mirkosertic/ESP8266Weatherstation/src/icons.h

#ifndef ICONS_H
#define ICONS_H

#include <Arduino.h>

// Bitmaps generated with https://javl.github.io/image2cpp/

// Icons with credits to https://github.com/manifestinteractive/weather-underground-icons/tree/master/

const unsigned char epd_bitmap_temperature[] PROGMEM = {
	0xff, 0xff, 0xff, 0xff, 0xff, 0xff, 0xff, 0xff, 0xff, 0xff, 0xff, 0xff, 0xff, 0xff, 0xff, 0xff,
	0xff, 0xf0, 0x3f, 0xff, 0xff, 0xe0, 0x1f, 0xff, 0xff, 0xc0, 0x0f, 0xff, 0xff, 0xc3, 0x0f, 0xff,
	0xff, 0xc7, 0x88, 0xff, 0xff, 0xc7, 0x88, 0xff, 0xff, 0xc7, 0x8f, 0xff, 0xff, 0xc7, 0x80, 0xff,
	0xff, 0xc7, 0x8f, 0xff, 0xff, 0xc4, 0x88, 0xff, 0xff, 0xc4, 0x88, 0xff, 0xff, 0xc4, 0x8f, 0xff,
	0xff, 0xc4, 0x88, 0xff, 0xff, 0xc4, 0x88, 0xff, 0xff, 0xc4, 0x87, 0xff, 0xff, 0x84, 0x87, 0xff,
	0xff, 0x84, 0xc3, 0xff, 0xff, 0x88, 0x43, 0xff, 0xff, 0x08, 0x43, 0xff, 0xff, 0x88, 0x43, 0xff,
	0xff, 0x87, 0x87, 0xff, 0xff, 0x80, 0x07, 0xff, 0xff, 0xc0, 0x0f, 0xff, 0xff, 0xe0, 0x1f, 0xff,
	0xff, 0xf8, 0x7f, 0xff, 0xff, 0xff, 0xff, 0xff, 0xff, 0xff, 0xff, 0xff, 0xff, 0xff, 0xff, 0xff};

const unsigned char epd_bitmap_hygrometer[] PROGMEM = {
	0xff, 0xff, 0xff, 0xff, 0xff, 0xff, 0xff, 0xff, 0xff, 0xff, 0xff, 0xff, 0xff, 0xff, 0xff, 0xff,
	0xff, 0xef, 0xfc, 0x3f, 0xff, 0xc7, 0xf8, 0x1f, 0xff, 0xc3, 0xff, 0x8f, 0xff, 0x83, 0xff, 0xcf,
	0xff, 0x91, 0xff, 0x8f, 0xff, 0x19, 0xff, 0x0f, 0xfe, 0x3c, 0xff, 0x0f, 0xfe, 0x7c, 0xff, 0xcf,
	0xfc, 0x7c, 0x7f, 0x8f, 0xfc, 0x00, 0x7f, 0x0f, 0xfc, 0x00, 0x3f, 0x0f, 0xf8, 0x00, 0x3f, 0xcf,
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
	0xfc, 0x00, 0x00, 0x1f, 0xff, 0x00, 0x00, 0x7f, 0xff, 0xff, 0xff, 0xff, 0xff, 0xff, 0xff, 0xff,
	0xff, 0xff, 0xff, 0xff, 0xff, 0xff, 0xff, 0xff, 0xff, 0xff, 0xff, 0xff, 0xff, 0xff, 0xff, 0xff};

#endif
