mirkosertic/ESP8266Weatherstation/src/display.cpp

#include "display.h"

#include <SPI.h>

#include "logging.h"
#include "icons.h"

#define ENABLE_GxEPD2_GFX 0

// ESP8266 CS(SS)=15,SCL(SCK)=14,SDA(MOSI)=13,BUSY=16,RES(RST)=5,DC=4

#include <GxEPD2_BW.h>
#include <GxEPD2_3C.h>
#include <GxEPD2_4C.h>
#include <GxEPD2_7C.h>
#include <Fonts/FreeMonoBold9pt7b.h>
#include <Fonts/FreeMonoBold18pt7b.h>
#include <Fonts/FreeMonoBold24pt7b.h>
#include <bitmaps/Bitmaps200x200.h> // 1.54" b/w

#include "GxEPD2_display_selection_new_style.h"
#include "GxEPD2_selection_check.h"

Display::Display()
{
}

void Display::init(bool fromdeepsleep)
{

    if (fromdeepsleep) {
        INFO("Init from deep sleep");        
        display.init(115200, false, 2, false); // USE THIS for Waveshare boards with "clever" reset circuit, 2ms reset pulse
    } else {
        INFO("Regular init");
        display.init(115200, true, 2, false); // USE THIS for Waveshare boards with "clever" reset circuit, 2ms reset pulse        
    }
    INFO("Init done");

    display.setRotation(1);
    INFO("Refresh");
    display.refresh();
    if (fromdeepsleep) {
        INFO("Refresh from deep sleep");
    } else {
        INFO("Refresh done");
    }
}

void Display::renderRightAligned(String text, int x, int y)
{
    int16_t tbx, tby;
    uint16_t tbw, tbh;
    display.getTextBounds(text, 0, 0, &tbx, &tby, &tbw, &tbh);

    display.setCursor(x - tbw - 1, y);
    display.print(text);
}

void Display::renderData(SensorData sensorData, bool fromdeepsleep)
{
    display.setFont(&FreeMonoBold24pt7b);
    display.setTextColor(GxEPD_BLACK);
    display.setFullWindow();
    display.fillScreen(GxEPD_WHITE);

    this->renderRightAligned(String((int)sensorData.indoorTemperature), 105, 35);
    this->renderRightAligned(String((int)sensorData.indoorHumidity), 105, 90);
    this->renderRightAligned(String((int)sensorData.outdoorTemperature), 105, 145);

    display.setFont(&FreeMonoBold18pt7b);
    display.setCursor(110, 85);
    display.print("%");

    display.setFont(&FreeMonoBold9pt7b);
    display.setCursor(113, 15);
    display.print("o");

    display.setCursor(113, 126);
    display.print("o");

    display.setCursor(135, 15);
    display.print("Min");
    display.setCursor(135, 35);
    display.print("Max");
    this->renderRightAligned(String((int)sensorData.indoorTemperatureMin), 199, 15);
    this->renderRightAligned(String((int)sensorData.indoorTemperatureMax), 199, 35);

    display.setCursor(135, 70);
    display.print("Min");
    display.setCursor(135, 90);
    display.print("Max");
    this->renderRightAligned(String((int)sensorData.indoorHumidityMin), 199, 70);
    this->renderRightAligned(String((int)sensorData.indoorHumidityMax), 199, 90);

    display.setCursor(135, 125);
    display.print("Min");
    display.setCursor(135, 145);
    display.print("Max");
    this->renderRightAligned(String((int)sensorData.outdoorTemperatureMin), 199, 125);
    this->renderRightAligned(String((int)sensorData.outdoorTemperatureMax), 199, 145);

    display.drawBitmap(0, 6, epd_bitmap_temperature, 32, 32, GxEPD_WHITE, GxEPD_BLACK);

    display.drawBitmap(0, 61, epd_bitmap_hygrometer, 32, 32, GxEPD_WHITE, GxEPD_BLACK);

    display.drawBitmap(0, 116, epd_bitmap_outdoor, 32, 32, GxEPD_WHITE, GxEPD_BLACK);

    display.setFont(&FreeMonoBold9pt7b);
    if (CLEAR_NIGHT == sensorData.forecast)
    {
        display.drawBitmap(0, 160, epd_bitmap_clear, 32, 32, GxEPD_WHITE, GxEPD_BLACK);
        display.setCursor(60, 175);
        display.print("Klar");
    }
    else if (CLOUDY == sensorData.forecast)
    {
        display.drawBitmap(0, 160, epd_bitmap_cloudy, 32, 32, GxEPD_WHITE, GxEPD_BLACK);
        display.setCursor(60, 175);
        display.print("Bewoelkt");
    }
    else if (FOG == sensorData.forecast)
    {
        display.drawBitmap(0, 160, epd_bitmap_fog, 32, 32, GxEPD_WHITE, GxEPD_BLACK);
        display.setCursor(60, 175);
        display.print("Nebelig");
    }
    else if (HAIL == sensorData.forecast)
    {
        display.drawBitmap(0, 160, epd_bitmap_flurries, 32, 32, GxEPD_WHITE, GxEPD_BLACK);
        display.setCursor(60, 175);
        display.print("Hagel");
    }
    else if (LIGHTING == sensorData.forecast)
    {
        display.drawBitmap(0, 160, epd_bitmap_tstorms, 32, 32, GxEPD_WHITE, GxEPD_BLACK);
        display.setCursor(60, 175);
        display.print("Gewitter");
    }
    else if (LIGHTING_RAINY == sensorData.forecast)
    {
        display.drawBitmap(0, 160, epd_bitmap_chancetstorms, 32, 32, GxEPD_WHITE, GxEPD_BLACK);
        display.setCursor(60, 175);
        display.print("Gewitter");
    }
    else if (PARTLY_CLOUDY == sensorData.forecast)
    {
        display.drawBitmap(0, 160, epd_bitmap_partlycloudy, 32, 32, GxEPD_WHITE, GxEPD_BLACK);
        display.setCursor(60, 175);
        display.print("Bewoelkt");
    }
    else if (POURING == sensorData.forecast)
    {
        display.drawBitmap(0, 160, epd_bitmap_rain, 32, 32, GxEPD_WHITE, GxEPD_BLACK);
        display.setCursor(60, 175);
        display.print("Regen");
    }
    else if (RAINY == sensorData.forecast)
    {
        display.drawBitmap(0, 160, epd_bitmap_chancerain, 32, 32, GxEPD_WHITE, GxEPD_BLACK);
        display.setCursor(60, 175);
        display.print("Regen");
    }
    else if (SNOWY == sensorData.forecast)
    {
        display.drawBitmap(0, 160, epd_bitmap_snow, 32, 32, GxEPD_WHITE, GxEPD_BLACK);
        display.setCursor(60, 175);
        display.print("Schnee");
    }
    else if (SNOW_RAINY == sensorData.forecast)
    {
        display.drawBitmap(0, 160, epd_bitmap_sleet, 32, 32, GxEPD_WHITE, GxEPD_BLACK);
        display.setCursor(60, 175);
        display.print("Schnee");
    }
    else if (SUNNY == sensorData.forecast)
    {
        display.drawBitmap(0, 160, epd_bitmap_sunny, 32, 32, GxEPD_WHITE, GxEPD_BLACK);
        display.setCursor(60, 175);
        display.print("Sonnig");
    }
    else if (WINDY == sensorData.forecast)
    {
        display.drawBitmap(0, 160, epd_bitmap_hazy, 32, 32, GxEPD_WHITE, GxEPD_BLACK);
        display.setCursor(60, 175);
        display.print("Windig");
    }
    else if (WINDY_VARIANT == sensorData.forecast)
    {
        display.drawBitmap(0, 160, epd_bitmap_cloudy, 32, 32, GxEPD_WHITE, GxEPD_BLACK);
        display.setCursor(60, 175);
        display.print("Windig");
    }
    else
    {
        display.drawBitmap(0, 160, epd_bitmap_unknown, 32, 32, GxEPD_WHITE, GxEPD_BLACK);
        display.setCursor(60, 175);
        display.print(sensorData.forecast);
    }

    display.setCursor(60, 195);
    display.print(sensorData.latestUpdateTime);

    INFO("Before display");
    display.display(fromdeepsleep);
    INFO("After display");

    display.hibernate();
}
